balthazar-space/Case-and-housing-design/v0.2/STL_Print_Case_v0.2/CASE_bottom_down_right.stl

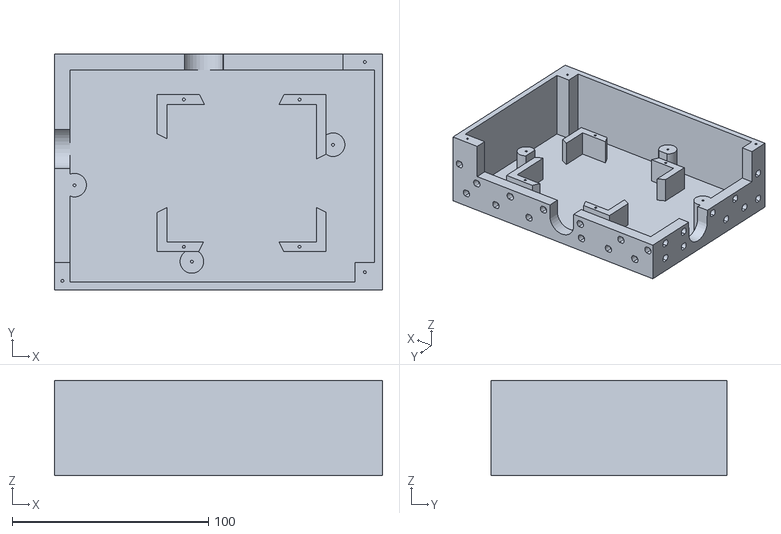
[picture p37: CAD file, 2023-08-29, an earlier design]
v0.2/STL_Print_Case_v0.2/CASE_bottom_down_right.stl
167.0 x 120.0 x 48.5
